ChasinSpin/astrid/3DPrinted/stl/cameraDob/cameraDobRings.stl

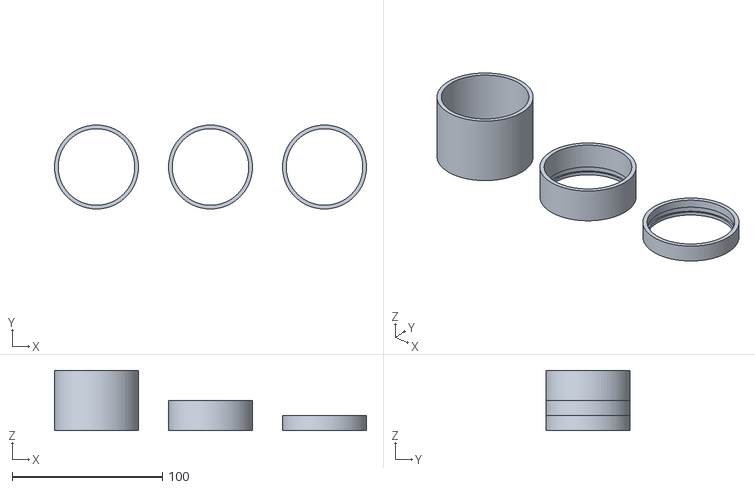
[picture p28: CAD file, 2024-11-13]
3DPrinted/stl/cameraDob/cameraDobRings.stl
208.0 x 56.0 x 40.0
