ChasinSpin/astrid/docs/images/assembly42.jpg

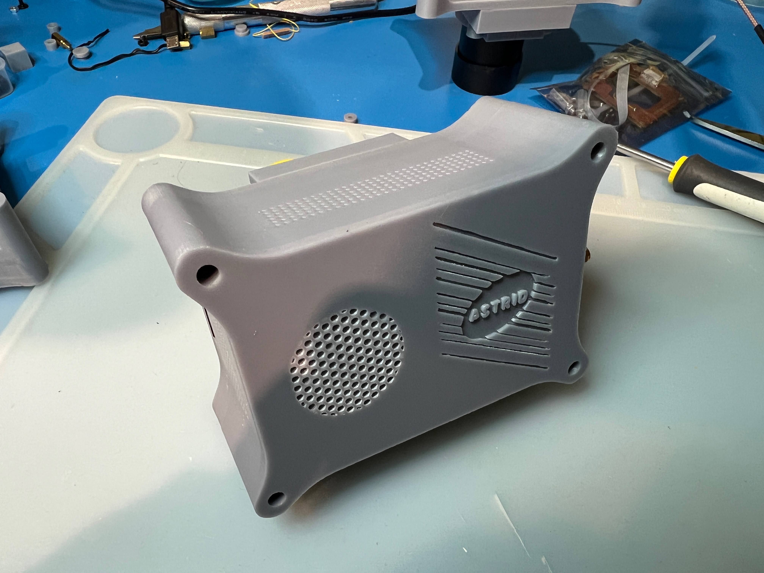
docs/images/assembly42.jpg
