ChasinSpin/astrid/OTEStamper/firmware/eeprom.h

extern void eepromInit(void);
extern uint16_t eepromReadVersion(void);
extern void eepromUpdateVersion(uint16_t v);
extern uint8_t eepromReadLeapSeconds(void);
extern void eepromUpdateLeapSeconds(uint8_t v);
