ChasinSpin/astrid/app/UiPanelObject.py

from processlogger import ProcessLogger
import os
import time
import math
import binascii
import subprocess
from UiPanel import UiPanel
from PyQt5.QtWidgets import QMessageBox, QVBoxLayout, QApplication
from astropy import units as u
from astropy.coordinates import SkyCoord, SphericalRepresentation
from settings import Settings
from astcoord import AstCoord
from astropy.time import Time
from astropy.coordinates.name_resolve import NameResolveError
from astropy.coordinates import solar_system_ephemeris, get_body_barycentric, get_body, cartesian_to_spherical
from UiPanelObjectAddEdit import UiPanelObjectAddEdit
from UiPanelObjectList import UiPanelObjectList
from UiPanelPrepoint import UiPanelPrepoint
from UiPanelAutoRecord import UiPanelAutoRecord
from UiPanelSatelliteGetTime import UiPanelSatelliteGetTime
from PyQt5.QtCore import Qt, QThread, pyqtSignal
from UiDialogPanel import UiDialogPanel
from UiPanelAutoRecording import UiPanelAutoRecording
from UiPanelSearchXMLPredictions import UiPanelSearchXMLPredictions
from datetime import datetime, timedelta
from astsite import AstSite
from pathcomputation import PathComputation
from owcloud import OWCloud
from astutils import AstUtils
from starcatalog import StarLookup, Star
from StarCatalogExtract import StarCatalogExtract
from satellite import Satellite



# Imports data from OWCloud via a seperate thread

class OWCloudThread(QThread):
	importFromOWCloudError		= pyqtSignal(str)
	importFromOWCloudSuccess	= pyqtSignal(str)

	def __init__(self):
		super(QThread, self).__init__()


	def run(self):
		owcloud		= OWCloud()
		(events, error) = owcloud.getEvents()

		imported_count = 0

		if error is not None:
			self.importFromOWCloudError.emit('Failed to download from OWCloud: %s' % error)
			return
		elif events is None:
			self.importFromOWCloudError.emit('Events = None from OWCloud')
			return
		elif len(events) > 0:
			occultations = Settings.getInstance().occultations['occultations']
			occultations_new = []

			# This removes all OWCloud occultations we have
			for i in range(len(occultations)):
				if not 'source' in occultations[i].keys() or occultations[i]['source'] != 'OWCloud':
					occultations_new.append(occultations[i])

			# Now we add the new occultations
			for occultation in events:
				# Add the occultation, but don't import expired occultations
				if datetime.strptime(occultation['event_time'], '%Y-%m-%dT%H:%M:%S') >= datetime.utcnow():
					occultations_new.append(occultation)
					imported_count += 1
					print(occultation)

			Settings.getInstance().occultations['occultations'] = occultations_new
			Settings.getInstance().writeSubsetting('occultations')

		owcloud = None
		self.importFromOWCloudSuccess.emit('Imported %d registered events/stations from OWCloud' % imported_count)


# Download Occelmnt Predictions on a seperate thread 

class DownloadPredictionsThread(QThread):
	downloadPredictionsStatus	= pyqtSignal(str)
	downloadPredictionsFinished	= pyqtSignal()

	def __init__(self, url):
		super(QThread, self).__init__()

		self.url = url


	def run(self):
		url = binascii.unhexlify(self.url).decode('ascii')
		bname = os.path.basename(url)
		download_path = Settings.getInstance().astrid_drive + '/' + bname

		self.downloadPredictionsStatus.emit('Downloading: %s\n\nplease wait...' % bname)

		
		cmd = ['/usr/bin/wget', '-O', download_path, url]
		print(cmd)
		subprocess.run(args=cmd)

		self.downloadPredictionsStatus.emit('Extracting: %s\n\nplease wait...' % bname)
		cmd = ['/usr/bin/tar', '--directory', Settings.getInstance().astrid_drive, '-xvf', download_path]
		print(cmd)
		subprocess.run(args=cmd)

		os.remove(download_path)

		self.downloadPredictionsFinished.emit()



class UiPanelObject(UiPanel):
	# Initializes and displays a Panel

	SEARCH_SIMBAD		= 'SIMBAD (online)'
	SEARCH_CUSTOM		= 'Custom'
	SEARCH_OCCULTATIONS	= 'Occultations'
	SEARCH_OCCULTGAIA	= 'Occult Gaia'
	SEARCH_SOLARSYSTEM	= 'Solar System'
	SEARCH_SATELLITES	= 'Satellites'
	PREDICTIONS_URL		= b'68747470733a2f2f6173747269642d646f776e6c6f6164732e73332e616d617a6f6e6177732e636f6d2f646f776e6c6f6164732f7374657665705f70726564696374696f6e735f323032335f323032345f76312e74787a'

	def __init__(self, camera):
		super().__init__('Object (ICRS)')
		self.processLogger = ProcessLogger.getInstance()
		self.logger = self.processLogger.getLogger()
		self.camera		= camera
		self.occultationObject	= None
		self.widgetDatabase	= self.addComboBox('Database', [self.SEARCH_SIMBAD, self.SEARCH_CUSTOM, self.SEARCH_OCCULTATIONS, self.SEARCH_OCCULTGAIA, self.SEARCH_SOLARSYSTEM, self.SEARCH_SATELLITES])
		self.widgetDatabase.setObjectName('comboBoxDatabase')
		self.widgetSearch	= self.addLineEdit('Search')
		self.widgetRA		= self.addLineEdit('RA', editable=False)
		self.widgetDEC		= self.addLineEdit('DEC', editable=False)
		self.widgetEventTime    = self.addLineEdit('Event Time', editable=False)
		self.widgetChord    	= self.addLineEdit('Chord Dist', editable=False)
		self.hideWidget(self.widgetEventTime)
		self.hideWidget(self.widgetChord)
		self.widgetPrepoint	= self.addButton('Prepoint', True)
		self.widgetAutoRecord	= self.addButton('Auto Record', True)
		self.hideWidget(self.widgetPrepoint)
		self.widgetAdd		= self.addButton('Add', True)
		self.widgetList		= self.addButton('List', True)
		self.hideWidget(self.widgetAdd)
		self.hideWidget(self.widgetList)

		# Set to Occultations by default
		self.widgetDatabase.setCurrentText(UiPanelObject.SEARCH_OCCULTATIONS)
		self.comboBoxDatabaseChanged(self.widgetDatabase.currentText())
		
		self.setColumnWidth(0, 75)
		self.setColumnWidth(1, 170)


	def registerCallbacks(self):
		self.widgetDatabase.currentTextChanged.connect(self.comboBoxDatabaseChanged)
		self.widgetSearch.editingFinished.connect(self.lineEditSearchChanged)
		self.widgetPrepoint.clicked.connect(self.buttonPrepointPressed)
		self.widgetAutoRecord.clicked.connect(self.buttonAutoRecordPressed)
		self.widgetAdd.clicked.connect(self.buttonAddPressed)
		self.widgetList.clicked.connect(self.buttonListPressed)

	
	# CALLBACKS

	def comboBoxDatabaseChanged(self, text):
		self.camera.clearObject()
		if   text == UiPanelObject.SEARCH_SIMBAD:
			self.hideWidget(self.widgetEventTime)
			self.hideWidget(self.widgetChord)
			self.hideWidget(self.widgetPrepoint)
			self.hideWidget(self.widgetAutoRecord)
			self.hideWidget(self.widgetAdd)
			self.hideWidget(self.widgetList)
		elif text == UiPanelObject.SEARCH_CUSTOM:
			self.hideWidget(self.widgetEventTime)
			self.hideWidget(self.widgetChord)
			self.hideWidget(self.widgetPrepoint)
			self.hideWidget(self.widgetAutoRecord)
			self.showWidget(self.widgetAdd)
			self.showWidget(self.widgetList)
		elif text == UiPanelObject.SEARCH_OCCULTATIONS:
			self.showWidget(self.widgetEventTime)
			self.showWidget(self.widgetChord)
			self.hideWidget(self.widgetPrepoint)
			self.hideWidget(self.widgetAutoRecord)
			self.showWidget(self.widgetAdd)
			self.showWidget(self.widgetList)
		elif text == UiPanelObject.SEARCH_OCCULTGAIA:
			self.hideWidget(self.widgetEventTime)
			self.hideWidget(self.widgetChord)
			self.hideWidget(self.widgetPrepoint)
			self.hideWidget(self.widgetAutoRecord)
			self.hideWidget(self.widgetAdd)
			self.hideWidget(self.widgetList)


			starCatalogExtract = StarCatalogExtract()
			starCatalogExtract.checkAndExtract()
		elif text == UiPanelObject.SEARCH_SOLARSYSTEM:
			self.hideWidget(self.widgetEventTime)
			self.hideWidget(self.widgetChord)
			self.hideWidget(self.widgetPrepoint)
			self.hideWidget(self.widgetAutoRecord)
			self.hideWidget(self.widgetAdd)
			self.hideWidget(self.widgetList)
		elif text == UiPanelObject.SEARCH_SATELLITES:
			self.hideWidget(self.widgetEventTime)
			self.hideWidget(self.widgetChord)
			self.hideWidget(self.widgetPrepoint)
			self.hideWidget(self.widgetAutoRecord)
			self.showWidget(self.widgetAdd)
			self.showWidget(self.widgetList)
		else:
			raise ValueError('Database not valid')


	def lineEditSearchChanged(self):
		# When a message box is launch during a line edit handler, the line edit loses focus,
		# casuing 2 editingFinished messages to be sent, using isModified to prevent double launching
		if self.widgetSearch.isModified():
			self.launchSearch()


	def buttonAddPressed(self):
		if self.widgetDatabase.currentText() == UiPanelObject.SEARCH_OCCULTATIONS:
			msgBox = QMessageBox()
			msgBox.setIcon(QMessageBox.Question)
			msgBox.setText('How would you like to Add an occultation?')
			msgBox.addButton('Manual Entry or Occelmnt', QMessageBox.AcceptRole)
			msgBox.addButton('Sync From OWCloud', QMessageBox.AcceptRole)
			msgBox.addButton("Search Occelmnt XML Lists", QMessageBox.AcceptRole)
			msgBox.setStandardButtons(QMessageBox.Cancel)
		
			ret = msgBox.exec()

			if   ret == 0:
				self.dialog = UiDialogPanel('Add Object (ICRS)', UiPanelObjectAddEdit, args = {'database': self.widgetDatabase.currentText(), 'camera': self.camera, 'editValues': None}, parent = self.camera.ui)
			elif ret == 1:
				ret2 = QMessageBox.information(self, ' ', 'To sync from OWCloud, the following are required:\n\n    1. Internet Connection\n    2. Valid OWCloud login/password/api key in settings/observer\n    3. Site(s) added to events in OWCloud\n\nNote 1: After registering a site on OWCloud, it may take a few minutes for the data to be downloadble.\n\nTHIS WILL REPLACE OCCULTATIONS WITH THE SAME NAME/STATION AND DELETE PREVIOUS EVENTS FROM OWCLOUD THAT NO LONGER EXIST.', QMessageBox.Ok | QMessageBox.Cancel)
				if ret2 == QMessageBox.Ok:
					observer = Settings.getInstance().observer
					if observer['owcloud_login'] is None or observer['owcloud_login'] == '' or observer['owcloud_password'] is None or observer['owcloud_password'] == '':
						QMessageBox.information(self, ' ', 'No login or password for OWCloud has been set!\n\nAdd OWCloud login/password to the Observer settings in Astrid.', QMessageBox.Ok)
						return
					if observer['owcloud_apikey'] is None or observer['owcloud_apikey'] == '':
						QMessageBox.information(self, ' ', 'No API Key for OWCloud has been set!\n\nOWCloud now requires your own Api Key.\n\nTo setup, after login in OWCloud, visit User Profile / User Permissions and verify your email.\n\nThen visit User Permissions again and copy the API Key to the API Key setting in the Observer settings in Astrid.', QMessageBox.Ok)
						return
					self.importFromOWCloud()
			elif ret == 2:
				predictions_folder = Settings.getInstance().predictions_folder
				if not os.path.isdir(predictions_folder) or len(os.listdir(predictions_folder)) == 0:
					ret3 = QMessageBox.information(self, ' ', 'Missing predictions data, download now? (requires internet connection))', QMessageBox.Yes | QMessageBox.No)
					if ret3 == QMessageBox.Yes:
						self.downloadPredictions()
					else:
						return

				self.dialog = UiDialogPanel("Search Occelmnt XML Lists", UiPanelSearchXMLPredictions, args = {})
		else:
			self.dialog = UiDialogPanel('Add Object (ICRS)', UiPanelObjectAddEdit, args = {'database': self.widgetDatabase.currentText(), 'camera': self.camera, 'editValues': None}, parent = self.camera.ui)


	def buttonListPressed(self):
		self.dialog = UiDialogPanel('List Objects - ' + self.widgetDatabase.currentText(), UiPanelObjectList, args = {'database': self.widgetDatabase.currentText(), 'camera': self.camera, 'selectListCallback': self.listSelect, 'editListCallback': self.editSelect}, parent = self.camera.ui)


	def buttonPrepointPressed(self):
		if not self.camera.ui.panelStatus.goForRecordingVideo():
			QMessageBox.critical(self, ' ', 'Status buttons must be Green to Prepoint!  Check GPS connection, update site and/or wait until signal is acquired.', QMessageBox.Ok)
			return

		if not self.camera.isPhotoMode():
			self.camera.ui.panelTask.switchModeTo('Photo')
		self.dialog = UiDialogPanel('Prepoint', UiPanelPrepoint, args = {'camera': self.camera, 'object': self.occultationObject}, parent = self.camera.ui, position=(20,20))


	def buttonAutoRecordPressed(self):
		if not self.camera.ui.panelStatus.goForRecordingVideo():
			QMessageBox.critical(self, ' ', 'Status buttons must be Green to AutoRecord!  Check GPS connection, update site and/or wait until signal is acquired.', QMessageBox.Ok)
			return

		if not self.camera.isOTEVideoMode():
			ret = QMessageBox.question(self, ' ', 'Auto Recording is only available when camera is in OTE Video Mode. Switch Mode To OTE Video?\n\nFrame rate is currently set to: %0.2f fps (%0.6fs exposures)\n\nVerify that this frame rate is what you want for OTE Video Mode, otherwise cancel, switch to OTE Video and change frame rate.' % (1.0/(self.camera.videoFrameDuration / 1000000.0), self.camera.videoFrameDuration / 1000000.0), QMessageBox.Yes | QMessageBox.Cancel)
			if ret == QMessageBox.Yes:
				self.camera.ui.panelTask.switchModeTo('OTE Video')
			else:
				return

		if self.camera.isOTEVideoMode():
			if self.camera.ui.videoFrameRateWarning():
				return

			if self.camera.ui.videoFrameRateTooSlowWarning(self.occultationObject['event_duration']):
				return

			if AstUtils.isProcessByNameRunning('chromium-browser'):
				ret = QMessageBox.warning(self, ' ', 'The Chromium Web Browser is running which will result in frames dropped in Astrid.  Do you wish to Kill Chromium?', QMessageBox.Yes | QMessageBox.Cancel)
				if ret == QMessageBox.Yes:
					AstUtils.killProcessesByName('chromium-browser')
					time.sleep(2)
				else:
					return

			self.logger.info('AutoRecord Dialog launched, but Start Auto Record not pressed yet')
			self.dialog = UiDialogPanel('Auto Record OTE', UiPanelAutoRecord, args = {'camera': self.camera, 'object': self.occultationObject}, parent = self.camera.ui)
			if self.dialog.result() == 1:
				start_time = self.dialog.dialog.panel.start_time
				end_time = self.dialog.dialog.panel.end_time
				event_time = datetime.strptime(self.occultationObject['event_time'], '%Y-%m-%dT%H:%M:%S')
				if end_time <= datetime.utcnow():
					self.logger.warning('End time is before now, old event, aborting auto record')
					QMessageBox.warning(self, ' ', 'End time is before now, old event, unable to record!', QMessageBox.Ok)
				else:
					self.logger.info('Started Auto Record')
					self.dialog = UiDialogPanel('Auto Recording', UiPanelAutoRecording, args = {'start_time': start_time, 'end_time': end_time, 'event_time': event_time, 'camera': self.camera}, parent = self.camera.ui, modal = True)


	# OPERATIONS

	def setRaDec(self, coord):
		ra = ''
		dec = ''
		if coord is not None:
			(ra, dec) = coord.raDecStrForSettingFormat('icrs')

		self.widgetRA.setText(ra)
		self.widgetDEC.setText(dec)


	def messageBoxSearchObjectSuccess(self, name, coord):
		save = False
		if self.widgetDatabase.currentText() == UiPanelObject.SEARCH_SIMBAD:
			save = True

		gotoCapable = Settings.getInstance().mount['goto_capable']

		if gotoCapable:
			buttons = QMessageBox.Yes | QMessageBox.No
			if save:
				buttons |= QMessageBox.Save
		else:
			if save:
				buttons = QMessageBox.Yes | QMessageBox.No
			else:
				buttons = QMessageBox.Ok

		if save:
			if gotoCapable:
				msg = 'Object found, goto or save to custom?'
			else:
				msg = 'Object found, save to custom?'
		else:
			if gotoCapable:
				msg = 'Object found, goto?'
			else:
				msg = 'Object found'

		ret = QMessageBox.question(self, ' ', msg, buttons)
		self.widgetSearch.setModified(True)
		if ret == QMessageBox.Yes:
			if not gotoCapable and save:
				self.addObjectToCustomDatabase(name, coord)
				return False
			return True
		elif ret == QMessageBox.Save:
			self.addObjectToCustomDatabase(name, coord)
			return False
		elif ret == QMessageBox.Ok:
			return True
		elif ret == QMessageBox.No:
			return False
		else:
			return False


	def addObjectToCustomDatabase(self, name, coord):
		customObjects = Settings.getInstance().objects['custom_objects']
		for object in customObjects:
			if object['name'] == name:
				self.messageBoxWriteCustomFailed()
				return

		(ra, dec) = coord.raDec360Deg('icrs')
		customObjects.append({"name": name, "ra": ra, "dec": dec})
		Settings.getInstance().writeSubsetting('objects')
		

	def messageBoxSearchObjectFailed(self):
		if self.widgetDatabase.currentText() == self.SEARCH_OCCULTGAIA:
			QMessageBox.information(self, ' ', 'Object not found !\n\nValid Formats:\n    HIP 117053\n    HIP 6911\n    UCAC4 451-000373\n    TYC 4212-1079-1\n    EDR3 2545442368322040320\n\nNote:\n    UCAC4 123-123456 (2nd number is zero padded)\n    TYC 1234-56789-1 (or -2 or -3), 56789 is NOT zero padded\n    EDR3 12345345348 (variable length number, not zero padded)')
		else:
			QMessageBox.information(self, ' ', 'Object not found !')


	def messageBoxWriteCustomFailed(self):
		QMessageBox.information(self, ' ', 'Object already exists in custom !')


	def findObject(self, search):
		text = self.widgetDatabase.currentText()
		if   text == UiPanelObject.SEARCH_SIMBAD:
			return self.findSimbadObject(search)
		elif text == UiPanelObject.SEARCH_CUSTOM:
			return self.findCustomObject(search)
		elif text == UiPanelObject.SEARCH_OCCULTATIONS:
			return self.findOccultationObject(search)
		elif text == UiPanelObject.SEARCH_OCCULTGAIA:
			return self.findStarCatalogObject(search)
		elif text == UiPanelObject.SEARCH_SOLARSYSTEM:
			return self.findSolarSystemObject(search)
		elif text == UiPanelObject.SEARCH_SATELLITES:
			return self.findSatelliteObject(search)
		else:
			raise ValueError('Database not valid')


	def findSimbadObject(self, search):
		""" Returns AstCoord, or None if not found """
		obj = None

		if self.objectInSolarSystem(search):
			QMessageBox.information(self, ' ', 'Simbad does not provide objects inside the solar system, please use the Solar System Database.')
			return

		self.camera.ui.indeterminateProgressBar(True)

		# Because we're not processing Qt events during the simbad request cos app.exec() isn't being run during
		app = QApplication.instance()
		app.processEvents()
		app.processEvents()

		try:
			coord_icrs = SkyCoord.from_name(search, frame='icrs')
			obj = AstCoord.from360Deg(coord_icrs.ra.value, coord_icrs.dec.value, 'icrs')
		except NameResolveError:
			print("Unable to find object")
			pass
		except Exception as e:
			print("Error: simbad error:", e)
			pass

		self.camera.ui.indeterminateProgressBar(False)

		return obj


	def findCustomObject(self, search):
		""" Returns AstCoord, or None if not found """
		obj = None
		if self.objectInSolarSystem(search):
			QMessageBox.information(self, ' ', 'Custom does not provide objects inside the solar system, please use the Solar System Database.')
			return

		customObjects = Settings.getInstance().objects['custom_objects']
		for object in customObjects:
			if object['name'].lower() == search.lower():
				obj = AstCoord.from360Deg(object['ra'], object['dec'], 'icrs')
				break
		return obj


	def findSatelliteObject(self, search):
		""" Returns AstCoord, or None if not found """
		obj = None

		satelliteObjects = Settings.getInstance().satellites['satellites']
		for object in satelliteObjects:
			if object['name'].lower() == search.lower():
				self.dialogS = UiDialogPanel('Enter Event Time', UiPanelSatelliteGetTime, args = {}, parent = self.camera.ui)
				if self.dialogS.result() == 1:
					event_time = self.dialogS.dialog.panel.event_time
				else:
					return

				event_time += '.000000'

				satellite = Satellite(object['name'], [object['tle_line1'], object['tle_line2']], event_time)
				obj = AstCoord.from360Deg(satellite.ra, satellite.dec, 'icrs')
				break
		return obj


	def findOccultationObject(self, search):
		""" Returns AstCoord, or None if not found """
		obj = None
		self.occultationObject = None
		customObjects = Settings.getInstance().occultations['occultations']
		for object in customObjects:
			if object['name'].lower() == search.lower():
				obj = AstCoord.from360Deg(object['ra'], object['dec'], 'icrs')
				vet = self.verifyEventTime(object)
				self.widgetEventTime.setText(object['event_time'])

				if vet is None:
					self.widgetChord.setText('Not Found')
				else:
					fullEventTime = vet[0]
					chordDist = vet[1]
					self.widgetChord.setText('%0.3f km' % (chordDist/1000.0))
					object['predicted_center_time_full'] = fullEventTime.strftime('%Y-%m-%dT%H:%M:%S.%f') 
					Settings.getInstance().writeSubsetting('occultations')

				self.occultationObject = object
				break

		if obj is not None:
			self.showWidget(self.widgetPrepoint)
			self.showWidget(self.widgetAutoRecord)

		return obj


	def findStarCatalogObject(self, search):
		""" Returns AstCoord, or None if not found """
		obj = None

		search = search.upper()

		okCatalogs = ['HIP ', 'UCAC4 ', 'TYC ', 'EDR3 ']
		validCatalog = False
		for cat in okCatalogs:
			if search.startswith(cat):
				validCatalog = True
				break
		if not validCatalog:
			ret3 = QMessageBox.information(self, ' ', 'Stars in the Occult Gaia catalog must start with HIP, UCAC4, TYC or EDR3.', QMessageBox.Ok)
			return None

		starLookup = StarLookup()
		try:
			star = starLookup.findStarById(search)
		except FileNotFoundError:
			star = None

		if star is not None:
			star.epochPropogateToJ2000()
			obj = star.coord

		return obj


	def findSolarSystemObject(self, search):
		""" Returns AstCoord, or None if not found """
		obj = None

		location = AstSite.location()
		now = Time(datetime.utcnow(), scale='utc', location = location)
		#now = Time( datetime(2000,1,1,12,0,0,0), scale='utc', location = location)
		with solar_system_ephemeris.set('builtin'):
			try:
				obj = get_body(search, now, location)
				#obj = get_body_barycentric(search, now)
			except KeyError:
				obj = None

		if obj is not None:
			#obj = obj.transform_to('icrs')
			#obj.representation = 'spherical'
			#obj = obj.represent_as(SphericalRepresentation)
			#print(obj)
			#obj = obj.transform_to('icrs')
			obj = AstCoord.from360Deg(ra=obj.ra.value, dec=obj.dec.value, frame='icrs')

		return obj


	def setEnabledUi(self, enable):
		self.widgetDatabase.setEnabled(enable)
		self.widgetSearch.setEnabled(enable)
		self.widgetRA.setEnabled(enable)
		self.widgetDEC.setEnabled(enable)
		self.widgetEventTime.setEnabled(enable)
		self.widgetChord.setEnabled(enable)
		self.widgetPrepoint.setEnabled(enable)
		self.widgetAutoRecord.setEnabled(enable)
		self.widgetList.setEnabled(enable)
		self.widgetAdd.setEnabled(enable)


	def launchSearch(self):
		self.widgetSearch.setModified(False)
		txt = self.widgetSearch.text()
		self.camera.searchObject(txt)


	def listSelect(self, item):
		self.widgetSearch.setText(item)
		self.launchSearch()


	def editSelect(self, item):
		editValues = None

		text = self.widgetDatabase.currentText()

		if text == UiPanelObject.SEARCH_CUSTOM:
			objects = Settings.getInstance().objects['custom_objects']
		elif text == UiPanelObject.SEARCH_OCCULTATIONS:
			objects = Settings.getInstance().occultations['occultations']
		elif text == UiPanelObject.SEARCH_SATELLITES:
			objects = Settings.getInstance().satellites['satellites']

		for object in objects:
			if object['name'] == item:
				editValues = object
				break
		
		self.dialog = UiDialogPanel('Edit Object (ICRS)', UiPanelObjectAddEdit, args = {'database': self.widgetDatabase.currentText(), 'camera': self.camera, 'editValues': editValues}, parent = self.camera.ui)

	
	def __convertStrTimeToDateTime(self, sTime):
		return datetime.strptime(sTime, '%Y-%m-%dT%H:%M:%S')

	def __convertDateTimeToStrTime(self, dt):
		return dt.strftime("%Y-%m-%dT%H:%M:%S")

	def verifyEventTime(self, object):
		if not ('occelmnt' in object) or len(object['occelmnt'].keys()) == 0:
			self.logger.info('No occelmnt data recorded in the occulation, unable to verify event time or chord')
			return None

		pathComp		= PathComputation(object['occelmnt'])
		timeAndChordForLoc	= pathComp.getTimeAndChordDistanceForLocation(AstSite.lat, AstSite.lon, AstSite.alt)

		if timeAndChordForLoc is None:
			self.logger.info('No Chord because star is not visible')
			return None
		else:
			database_eventTime = self.__convertStrTimeToDateTime(object['event_time'])
			database_startTime = self.__convertStrTimeToDateTime(object['start_time'])
			database_endTime   = self.__convertStrTimeToDateTime(object['end_time'])

			deltaTimeSeconds = (timeAndChordForLoc[0] - database_eventTime).total_seconds()
			self.logger.info('Time: %s Distance: %0.4f km' % (str(timeAndChordForLoc[0]), timeAndChordForLoc[1] / 1000.0) )

			if abs(deltaTimeSeconds) >= 1:
				ret = QMessageBox.question(self, ' ', 'Event Center Time for this location differs from the one stored by %d seconds, do you wish to update start/center/end times to match?' % deltaTimeSeconds, QMessageBox.Yes | QMessageBox.No)
				if ret == QMessageBox.Yes:
					database_eventTime += timedelta(seconds=deltaTimeSeconds)
					database_startTime += timedelta(seconds=deltaTimeSeconds)
					database_endTime   += timedelta(seconds=deltaTimeSeconds)

					object['event_time'] = self.__convertDateTimeToStrTime(database_eventTime)
					object['start_time'] = self.__convertDateTimeToStrTime(database_startTime)
					object['end_time']   = self.__convertDateTimeToStrTime(database_endTime)

					db = 'occultations'
					all_occultations = Settings.getInstance().occultations['occultations']
					for o in all_occultations:
						if o['name'] == object['name']:
							o['event_time'] = object['event_time']
							o['start_time'] = object['start_time']
							o['end_time']   = object['end_time']
							Settings.getInstance().writeSubsetting(db)
							self.logger.info('updated %s' % (o['name']))
							break

		return timeAndChordForLoc


	def __importFromOWCloudError(self, txt):
		print('IERROR')
		self.importFromOWCloudMsgBox.done(0)
		QMessageBox.warning(self, ' ', txt, QMessageBox.Ok)
		self.importFromOWCloudMsgBox = None
		self.thread.wait()
		self.thread = None


	def __importFromOWCloudSuccess(self, txt):
		print('ISUCCESS')
		self.importFromOWCloudMsgBox.done(0)
		QMessageBox.information(self, ' ', txt, QMessageBox.Ok)
		self.importFromOWCloudMsgBox = None
		self.thread.wait()
		self.thread = None


	def importFromOWCloud(self):
		self.thread = OWCloudThread()
		self.thread.importFromOWCloudError.connect(self.__importFromOWCloudError)
		self.thread.importFromOWCloudSuccess.connect(self.__importFromOWCloudSuccess)
		#self.thread.finished.connect(self.thread.deleteLater)
		self.thread.start()

		self.importFromOWCloudMsgBox = QMessageBox()
		self.importFromOWCloudMsgBox.setIcon(QMessageBox.Information)
		self.importFromOWCloudMsgBox.setText('Please wait, downloading from OWCloud...')
		self.importFromOWCloudMsgBox.setStandardButtons(QMessageBox.NoButton)
		
		self.importFromOWCloudMsgBox.exec()


	def __downloadPredictionsStatus(self, txt):
		self.downloadPredictionsMsgBox.setText(txt)


	def __downloadPredictionsFinished(self):
		self.downloadPredictionsMsgBox.done(0)
		self.downloadPredictionsMsgBox = None
		self.thread2.wait()
		self.thread2 = None


	def downloadPredictions(self):
		self.thread2 = DownloadPredictionsThread(self.PREDICTIONS_URL)
		self.thread2.downloadPredictionsStatus.connect(self.__downloadPredictionsStatus)
		self.thread2.downloadPredictionsFinished.connect(self.__downloadPredictionsFinished)
		#self.thread2.finished.connect(self.thread2.deleteLater)
		self.thread2.start()

		self.downloadPredictionsMsgBox = QMessageBox()
		self.downloadPredictionsMsgBox.setIcon(QMessageBox.Information)
		self.downloadPredictionsMsgBox.setText('Download predictions...')
		self.downloadPredictionsMsgBox.setStandardButtons(QMessageBox.NoButton)
		
		self.downloadPredictionsMsgBox.exec()


	def objectInSolarSystem(self, search):
		if search.lower() in ['sun', 'mercury', 'venus', 'earth', 'moon', 'mars', 'jupiter', 'saturn', 'uranus', 'neptune', 'pluto']:
			return True
		return False
